wagiminator/ATmega-Soldering-Station/software/UI_upgrade_by_createskyblue/img/J3F}W4XX_3]NT2K_JGCY}(J.jpg

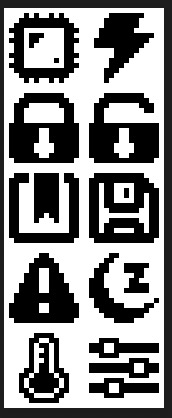
software/UI_upgrade_by_createskyblue/img/J3F}W4XX_3]NT2K_JGCY}(J.jpg
