wagiminator/ATmega-Soldering-Station/software/UI_upgrade_by_createskyblue/img/PixeSymbol3字符映射表.png

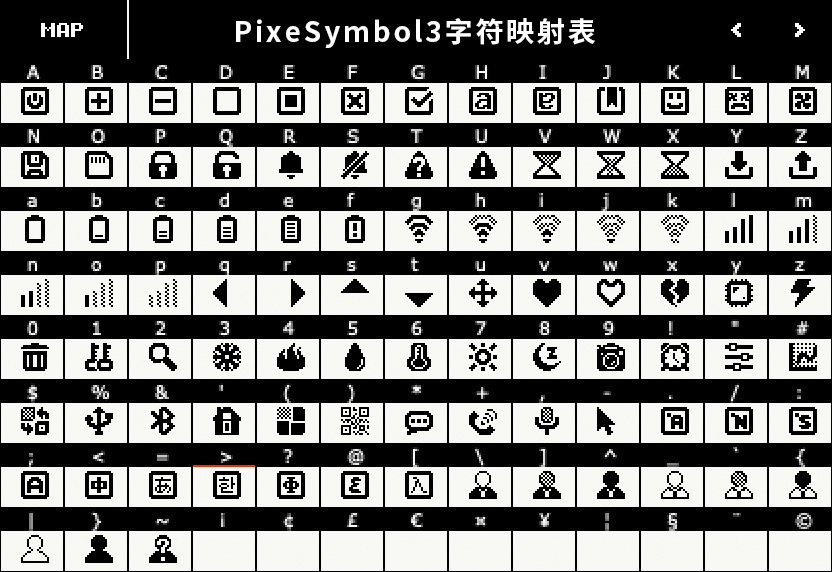
software/UI_upgrade_by_createskyblue/img/PixeSymbol3字符映射表.png
