wagiminator/ATmega-Soldering-Station/software/UI_upgrade_by_createskyblue/Program/1.8/1.8t4/1.8t4.ino

/*License: http://creativecommons.org/licenses/by-sa/3.0/
   采用CC3.0协议共享此程序
   您可以自由地
  共享 — 在任何媒介以任何形式复制、发行本作品
  演绎 — 修改、翻译或以本作品为基础进行创作
  在任何用途下，甚至商业目的。
  本许可协议为“自由文化作品（Free Cultural Works）”所接受。
  只要你遵守许可协议条款，许可人就无法收回你的这些权利。

  Attribution-ShareAlike 3.0 Unported (CC BY-SA 3.0)
  This is a human-readable summary of (and not a substitute for) the license. Disclaimer.
  You are free to:
  Share — copy and redistribute the material in any medium or format
  Adapt — remix, transform, and build upon the material
  for any purpose, even commercially.
  This license is acceptable for Free Cultural Works.
  The licensor cannot revoke these freedoms as long as you follow the license terms.
*/
// SolderingStation2
//
// ATmega328-controlled Soldering Station for Hakko T12 Tips.
// 此v1.8t4版本功能简介
// This 1.8t4 version of the code implements:
// - 烙铁头温度实时监测
// - Temperature measurement of the tip
// - PID温度控制
// - Direct or PID control of the heater
// - 可以通过编码器进行控制温度
// - Temperature control via rotary encoder
// - 短按编码器进入短时升温模式
// - Boost mode by short pressing rotary encoder switch
// - 长按编码器进入主菜单
// - Setup menu by long pressing rotary encoder switch
// - 手柄震动检测（需要手柄含有震动传感器）
// - Handle movement detection (by checking ball switch)
// - 手柄连接检测（通过判断烙铁头温度是否能够被读取来实现）
// - Iron unconnected detection (by idenfying invalid temperature readings)
// - 定时器设定 - 随眠，关机时间
// - Time driven sleep/power off mode if iron is unused (movement detection)
// - 可以测量主控芯片电压以及温度
// - Measurement of input voltage, Vcc and ATmega's internal temperature
// - 在OLED上实现信息显示
// - Information display on OLED
// - 支持无源蜂鸣器
// - Buzzer
// - 允许设置不同烙铁头的温度校准值
// - Calibrating and managing different soldering tips
// - 设置被保存在EEPROM，掉电不丢失
// - Storing user settings into the EEPROM
// - 允许热插拔烙铁头，并弹出烙铁头配置选择菜单
// - Tip change detection
// - 芯片过热以及低电压报警
// - Chip overheating and low voltage alarm
// - 更好的实时温度条以及实时功率条
// - Better real-time temperature bar and real-time power bar
// - 拥有过渡动画
// - Have transition animation
// - 内置屏幕保护程序
// - Built in screen saver
// - 屏幕翻转设置
// - Screen flip settings
// - 内置英文、中文、日文语言包
// - Built in English, Chinese and Japanese language pack
// - 开机密码设置
// - System Password
// - 允许设置旋钮方向
// - Knob direction setting menu
// - 内嵌看门狗，宕机自动重启
// - Watchdog timer automatic reset the MCU

// Power supply should be in the range of 16V/2A to 24V/3A and well
// stabilized.
//
// For calibration you need a soldering iron tips thermometer. For best results
// wait at least three minutes after switching on the soldering station before
// you start the calibration process.
//
// Controller:  ATmega328p
// Core:        Barebones ATmega (https://github.com/carlosefr/atmega)
// Clockspeed:  16 MHz external
//
// 2019/2020 by Stefan Wagner with great support from John Glavinos
// 2020-8 UI upgrade by LHW-createskyblue 、lihaoyun6
// Project Page: https://easyeda.com/wagiminator

//关于界面-项目页面二维码 ->为了加入欠压报警只能阉割掉关于页面的二维码
//const unsigned char QRCode[] PROGMEM = { 0x00, 0x00, 0x3e, 0x0e, 0x7c, 0x0c, 0x00, 0x00, 0x00, 0x00, 0x3e, 0x0e, 0x7c, 0x0c, 0x00, 0x00, 0x00, 0x00, 0x3e, 0x0e, 0x7c, 0x0c, 0x00, 0x00, 0x1f, 0xfe, 0x3f, 0xc1, 0x8c, 0x0c, 0x7f, 0xf8, 0x1f, 0xfe, 0x3f, 0xc1, 0x8c, 0x0c, 0x7f, 0xf8, 0x18, 0x06, 0x30, 0x01, 0xf3, 0x8c, 0x60, 0x18, 0x18, 0x06, 0x30, 0x01, 0xf3, 0x8c, 0x60, 0x18, 0x18, 0x06, 0x30, 0x01, 0xf3, 0x8c, 0x60, 0x18, 0x18, 0x06, 0x3e, 0x0f, 0xf0, 0x0c, 0x60, 0x18, 0x18, 0x06, 0x3e, 0x0f, 0xf0, 0x0c, 0x60, 0x18, 0x18, 0x06, 0x3f, 0xc1, 0xf0, 0x0c, 0x60, 0x18, 0x18, 0x06, 0x3f, 0xc1, 0xf0, 0x0c, 0x60, 0x18, 0x18, 0x06, 0x3f, 0xc1, 0xf0, 0x0c, 0x60, 0x18, 0x1f, 0xfe, 0x3e, 0x30, 0x70, 0x0c, 0x7f, 0xf8, 0x1f, 0xfe, 0x3e, 0x30, 0x70, 0x0c, 0x7f, 0xf8, 0x00, 0x00, 0x31, 0xce, 0x73, 0x8c, 0x00, 0x00, 0x00, 0x00, 0x31, 0xce, 0x73, 0x8c, 0x00, 0x00, 0x00, 0x00, 0x31, 0xce, 0x73, 0x8c, 0x00, 0x00, 0xff, 0xff, 0xf0, 0x01, 0x83, 0x8f, 0xff, 0xff, 0xff, 0xff, 0xf0, 0x01, 0x83, 0x8f, 0xff, 0xff, 0x00, 0xc0, 0x01, 0xc1, 0x8c, 0x00, 0x7f, 0x1f, 0x00, 0xc0, 0x01, 0xc1, 0x8c, 0x00, 0x7f, 0x1f, 0x00, 0xc0, 0x01, 0xc1, 0x8c, 0x00, 0x7f, 0x1f, 0x07, 0xc7, 0xcf, 0xce, 0x7f, 0x8c, 0x1f, 0xf8, 0x07, 0xc7, 0xcf, 0xce, 0x7f, 0x8c, 0x1f, 0xf8, 0x07, 0xc7, 0xcf, 0xce, 0x7f, 0x8c, 0x1f, 0xf8, 0xf8, 0x00, 0x3e, 0x3e, 0x03, 0xf0, 0x7f, 0x00, 0xf8, 0x00, 0x3e, 0x3e, 0x03, 0xf0, 0x7f, 0x00, 0xe0, 0xc7, 0xcf, 0xfe, 0x03, 0x80, 0x1f, 0xe7, 0xe0, 0xc7, 0xcf, 0xfe, 0x03, 0x80, 0x1f, 0xe7, 0xe0, 0xc7, 0xcf,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
const unsigned char Lang_JP[] PROGMEM = { 0x80, 0x04, 0x00, 0x00, 0x3f, 0xf0, 0x3d, 0xf0, 0x20, 0x10, 0x3b, 0xf0, 0x3b, 0x70, 0x30, 0x30, 0x2b, 0x50, 0x2a, 0xd0, 0x31, 0xb0, 0x3f, 0xf0, 0x00, 0x00, 0x80, 0x04 };
const unsigned char Save[] PROGMEM = { 0x00, 0x04, 0x58, 0x08, 0x58, 0x08, 0x58, 0x08, 0x40, 0x08, 0x7f, 0xf8, 0x60, 0x18, 0x5f, 0xe8, 0x5b, 0x68, 0x5f, 0xe8, 0x5b, 0x68, 0x1c, 0xe8, 0x5f, 0xe8, 0x00, 0x00 };
const unsigned char Lock[] PROGMEM = { 0xe0, 0x1c, 0xc0, 0x0c, 0x8f, 0xc4, 0x9f, 0xe4, 0x9f, 0xe4, 0x9f, 0xe4, 0x00, 0x00, 0x03, 0x00, 0x03, 0x00, 0x03, 0x00, 0x07, 0x80, 0x07, 0x80, 0x03, 0x00, 0x80, 0x04 };
const unsigned char Set19[] PROGMEM = { 0xf8, 0x7c, 0x80, 0x04, 0xbc, 0xf4, 0x3f, 0xf0, 0x38, 0x70, 0xb7, 0xb4, 0xb6, 0xb4, 0xb5, 0xb4, 0xb7, 0xb4, 0x38, 0x70, 0x3f, 0xf0, 0xbc, 0xf4, 0x80, 0x04, 0xf8, 0x7c };
const unsigned char *Ico_table[] = {
  Set0, Set1, Set2, Set3, Set4, Set5, Set19, Set6, Lock, Set_LANG, QRC, Set7,
  Set8, Set9, Set0, Set10, Set12, Save,
  Set0, Set11, Set14, Save,
  Set11, Set13, Set14, Save,
  Set15, Set16,
  Set17, Set18, //5
  Set5_1, Set5,
  c_NO, Set7,
  Lang_CN, Lang_EN, Lang_JP, //8
  Set4, Set4F, Save,
};
const byte Menu_table[] = {12, 6, 4, 4, 2, 2, 2, 2, 3, 3}; //菜单 标签 温控 定时 控制方式 首页 蜂鸣器 标签删除确认界面 语言菜单 翻转 显示
byte MenuLevel = 0; //菜单层级

/*////////////////////////////////////////////////////////////////////////////////////////////////////
   多语言支持
   Multilingual support
   ///////////////////////////////////////////////////////////////////////////////////////////////////
*/
/*
    英语库  ENGLISH
*/
const char EN_0[] PROGMEM = "Tip";
const char EN_1[] PROGMEM = "Temp";
const char EN_2[] PROGMEM = "Timer";
const char EN_3[] PROGMEM = "Control";
const char EN_4[] PROGMEM = "Screen";
const char EN_5[] PROGMEM = "Buzzer";
const char EN_6[] PROGMEM = "LOW Vol";
const char EN_7[] PROGMEM = "Lang";
const char EN_8[] PROGMEM = "Return";
const char EN_9[] PROGMEM = "Change";
const char EN_10[] PROGMEM = "Calibrate";
const char EN_11[] PROGMEM = "Rename";
const char EN_12[] PROGMEM = "Delete";
const char EN_13[] PROGMEM = "Add";
const char EN_14[] PROGMEM = "Save";
const char EN_15[] PROGMEM = "Default";
const char EN_16[] PROGMEM = "Sleep";
const char EN_17[] PROGMEM = "Boost";
const char EN_18[] PROGMEM = "Save";
const char EN_19[] PROGMEM = "Sleep";
const char EN_20[] PROGMEM = "Off";
const char EN_21[] PROGMEM = "Boost";
const char EN_22[] PROGMEM = "Save";
const char EN_23[] PROGMEM = "Direct";
const char EN_24[] PROGMEM = "PID";
const char EN_25[] PROGMEM = "Big";
const char EN_26[] PROGMEM = "Infos";
const char EN_27[] PROGMEM = "OFF";
const char EN_28[] PROGMEM = "ON";
const char EN_29[] PROGMEM = "NO";
const char EN_30[] PROGMEM = "YES";
const char EN_31[] PROGMEM = "CN";
const char EN_32[] PROGMEM = "EN";
const char EN_33[] PROGMEM = "NO";
const char EN_34[] PROGMEM = "OK";
const char EN_35[] PROGMEM = "Main Screen";
const char EN_36[] PROGMEM = "Flip";
const char EN_37[] PROGMEM = "Save";
const char EN_38[] PROGMEM = "About";
const char EN_39[] PROGMEM = "JP";
const char EN_40[] PROGMEM = "Lock";
const char EN_41[] PROGMEM = "Rotary";
const char *const EN_table[] PROGMEM = {EN_0, EN_1, EN_2, EN_3, EN_4, EN_5, EN_41, EN_6, EN_40, EN_7, EN_38, EN_8, EN_9, EN_10, EN_11, EN_12, EN_13, EN_14, EN_15, EN_16, EN_17, EN_18, EN_19, EN_20, EN_21, EN_22, EN_23, EN_24, EN_25, EN_26, EN_27, EN_28, EN_29, EN_30, EN_31, EN_32, EN_39, EN_35, EN_36, EN_37,};

/*
  #!/usr/bin/python
  # -*- coding: UTF-8 -*-
  for num in range(0,38):
  print("EN_",end="")
  print(num,end='')
  print(",",end="")
*/
/*
    中文语言库 CHINESE

  ////////////////////////////////////////////////////////////////////////////////////////////////////////
   本地化提示：你可以按照位图的大小，把这里的文字位图替换成你的语言，确保位图分辨率一致即可，我们欢迎你把程序翻译为你当地的语言！
  Localization tips: you can according to the size of the bitmap,
  replace the text bitmap here with your language,
  ensure that the bitmap resolution is consistent,
  we welcome you to translate the program into your local language!
  ////////////////////////////////////////////////////////////////////////////////////////////////////////
*/
//width:28,height:14 主界面中文提示
//Main Screen
//错误-ERROR
const unsigned char S1[] PROGMEM = { 0x20, 0x92, 0x1f, 0xc0, 0x3d, 0xf9, 0x90, 0x40, 0x20, 0x90, 0x90, 0x40, 0x40, 0x90, 0x1f, 0xc0, 0x7b, 0xff, 0x00, 0x00, 0xa0, 0x01, 0x3f, 0xe0, 0x21, 0xf9, 0x02, 0x00, 0xfd, 0x09, 0x02, 0x00, 0x21, 0x09, 0x7f, 0xf0, 0x21, 0xf9, 0x05, 0x00, 0x21, 0x09, 0x45, 0x00, 0x29, 0x09, 0x88, 0x80, 0x31, 0xf9, 0x10, 0x70, 0x21, 0x08, 0x20, 0x20 };
//关机-OFF
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
};
/*
  プリセット
  温度調節
  タイマー
  コントロール
  スクリーン
  ブザー
  低電圧アラーム
  言語
  戻る
  取り替える
  キャリブレーション
  名前を変更
  削除
  追加
  保存
  デフォルト
  睡眠
  ブースト
  保存
  睡眠
  閉じる
  ブースト
  保存
  ダイレクト
  PID
  ビッグ
  ニュース
  閉じる
  開く
  いいえ、
  はい、
  中国語
  英語
  いいえ、
  はい、
  メインスクリーン
  フリップ
  保存
  アバウト
  日本語
  つまみ方向

  汉字转换表:温度調節低電圧言語戻取替名前変更削除追加保存睡眠閉開中国英日本密碼
*/
const char JP_0[] PROGMEM  = { 0xf0, 0xcc, 0xdf, 0xb0, 0xb8, 0xbd, };
const char JP_1[] PROGMEM  = { 0xf2, 0x00, 0x01, 0x02, 0x03, };
const char JP_2[] PROGMEM  = { 0xf0, 0xb4, 0x99, 0xd3, 0xee, };
const char JP_3[] PROGMEM  = { 0xf0, 0xa8, 0xe8, 0xbd, 0xe2, 0xee, 0xe0, };
const char JP_4[] PROGMEM  = { 0xf0, 0xae, 0xa4, 0xdf, 0xee, 0xe8, };
const char JP_5[] PROGMEM  = { 0xf0, 0xcb, 0xab, 0xee, };
const char JP_6[] PROGMEM  = { 0xf2, 0x04, 0x05, 0x06, 0xf0, 0x97, 0xde, 0xee, 0xd5, };
const char JP_7[] PROGMEM  = { 0xf2, 0x07, 0x08, };
const char JP_8[] PROGMEM  = { 0xf2, 0x09, 0xf0, 0x8d, };
const char JP_9[] PROGMEM  = { 0xf2, 0x0a, 0xf0, 0x8c, 0xf2, 0x0b, 0xf0, 0x4a, 0x8d, };
const char JP_10[] PROGMEM = { 0xf0, 0xa2, 0xd8, 0xdf, 0xcb, 0xe1, 0xee, 0xac, 0xdc, 0xe8, };
const char JP_11[] PROGMEM = { 0xf2, 0x0c, 0x0d, 0xf0, 0x94, 0xf2, 0x0e, 0x0f, };
const char JP_12[] PROGMEM = { 0xf2, 0x10, 0x11, };
const char JP_13[] PROGMEM = { 0xf2, 0x12, 0x13, };
const char JP_14[] PROGMEM = { 0xf2, 0x14, 0x15, };
const char JP_15[] PROGMEM = { 0xf0, 0xbc, 0xca, 0x9e, 0xe0, 0xbd, };
const char JP_16[] PROGMEM = { 0xf2, 0x16, 0x17, };
const char JP_17[] PROGMEM = { 0xf0, 0xcb, 0xee, 0xae, 0xbd, };
const char JP_18[] PROGMEM = { 0xf2, 0x14, 0x15, };
const char JP_19[] PROGMEM = { 0xf2, 0x16, 0x17, };
const char JP_20[] PROGMEM = { 0xf2, 0x18, 0xf0, 0x5a, 0x8d, };
const char JP_21[] PROGMEM = { 0xf0, 0xcb, 0xee, 0xae, 0xbd, };
const char JP_22[] PROGMEM = { 0xf2, 0x14, 0x15, };
const char JP_23[] PROGMEM = { 0xf0, 0xb5, 0x99, 0xe1, 0xa4, 0xbd, };
const char JP_24[] PROGMEM = { 0xf1, 0x30, 0x29, 0x24, };
const char JP_25[] PROGMEM = { 0xf0, 0xc8, 0xb8, 0xa5, };
const char JP_26[] PROGMEM = { 0xf0, 0xc0, 0xda, 0xee, 0xae, };
const char JP_27[] PROGMEM = { 0xf2, 0x18, 0xf0, 0x5a, 0x8d, };
const char JP_28[] PROGMEM = { 0xf2, 0x19, 0xf0, 0x51, };
const char JP_29[] PROGMEM = { 0xf0, 0x46, 0x46, 0x4a, 0x01, };
const char JP_30[] PROGMEM = { 0xf0, 0x71, 0x46, 0x01, };
const char JP_31[] PROGMEM = { 0xf2, 0x1a, 0x1b, 0x08, };
const char JP_32[] PROGMEM = { 0xf2, 0x1c, 0x08, };
const char JP_33[] PROGMEM = { 0xf0, 0x46, 0x46, 0x4a, 0x01, };
const char JP_34[] PROGMEM = { 0xf0, 0x71, 0x46, 0x01, };
const char JP_35[] PROGMEM = { 0xf0, 0xd6, 0x99, 0xe8, 0xae, 0xa4, 0xdf, 0xee, 0xe8, };
const char JP_36[] PROGMEM = { 0xf0, 0xca, 0xdf, 0xb8, 0xcc, };
const char JP_37[] PROGMEM = { 0xf2, 0x14, 0x15, };
const char JP_38[] PROGMEM = { 0xf0, 0x97, 0xc5, 0x9b, 0xbd, };
const char JP_39[] PROGMEM = { 0xf2, 0x1d, 0x1e, 0x08, };
const char JP_40[] PROGMEM = { 0xf2, 0x1f, 0x20, }; //密码
const char JP_41[] PROGMEM = { 0xf0, 0x66, 0x80, 0x81, 0xf2, 0x21, 0x22, }; //つまみ方向
const char *const JP_table[] = {JP_0, JP_1, JP_2, JP_3, JP_4, JP_5, JP_41, JP_6, JP_40, JP_7, JP_38, JP_8, JP_9, JP_10, JP_11, JP_12, JP_13, JP_14, JP_15, JP_16, JP_17, JP_18, JP_19, JP_20, JP_21, JP_22, JP_23, JP_24, JP_25, JP_26, JP_27, JP_28, JP_29, JP_30, JP_31, JP_32, JP_39, JP_35, JP_36, JP_37,};
const char JP_Length_table[] PROGMEM = {6, 5, 5, 7, 6, 4, 7, 9, 3, 3 , 5, 4, 9, 10, 8, 3, 3, 3, 6, 3, 5, 3, 3, 5, 5, 3, 6, 4, 4, 5, 5, 4, 5, 4, 4, 3, 4,  9, 5, 3,};

#endif

bool lastbutton;
#include <Arduboy2.h>  //注意 这里使用被阉割的图形库，只有绘图功能，并非通用的版本
Arduboy2 arduboy;

#include <EEPROM.h>
#include <PID_v1.h>
#include <avr/sleep.h>

// Firmware version
#define VERSION       "v1.8t4"

// Type of rotary encoder
#define ROTARY_TYPE   1         // 0: 2 increments/step; 1: 4 increments/step

// Pins
#define SENSOR_PIN    A0        // temperature sense
#define VIN_PIN       A1        // input voltage sense
#define BUZZER_PIN     5        // buzzer
#define BUTTON_PIN     6        // rotary encoder switch
#define ROTARY_1_PIN   7        // rotary encoder 1
#define ROTARY_2_PIN   8        // rotary encoder 2
#define CONTROL_PIN    9        // heater MOSFET PWM control
#define SWITCH_PIN    10        // handle vibration switch

// Default temperature control values (recommended soldering temperature: 300-380°C)
#define ChipTempCalVal 335  //芯片内部温度读取校准值 -->可以根据实际情况修改，不同机器情况不同，通常误差在10°C内
#define TEMP_MIN      150       // min selectable temperature
#define TEMP_MAX      400       // max selectable temperature
#define TEMP_DEFAULT  320       // default start setpoint
#define TEMP_SLEEP    150       // temperature in sleep mode
#define TEMP_BOOST     60       // temperature increase in boost mode
#define TEMP_STEP      10       // rotary encoder temp change steps

// Default tip temperature calibration values
#define TEMP200       216       // temperature at ADC = 200
#define TEMP280       308       // temperature at ADC = 280
#define TEMP360       390       // temperature at ADC = 360
#define TEMPCHP       30        // chip temperature while calibration
#define TIPMAX        8         // max number of tips
#define TIPNAMELENGTH 6         // max length of tip names (including termination)
#define TIPNAME       "BC1.5"   // default tip name

// Default timer values (0 = disabled)
#define TIME2SLEEP     5        // time to enter sleep mode in minutes
#define TIME2OFF      15        // time to shut off heater in minutes
#define TIMEOFBOOST   40        // time to stay in boost mode in seconds

// Control values
#define TIME2SETTLE   950       // time in microseconds to allow OpAmp output to settle
#define SMOOTHIE      0.05      // OpAmp output smooth factor (1=no smoothing; 0.05 default)
#define PID_ENABLE    true      // enable PID control
#define BEEP_ENABLE   true      // enable/disable buzzer
#define MAINSCREEN    1         // type of main screen (0: big numbers; 1: more infos)

// EEPROM identifier
#define EEPROM_IDENT   0x140A   // to identify if EEPROM was written by this program

//Beep
#define SetBeepCoolTime 200
unsigned long BeepCoolTime;

// Define the aggressive and conservative PID tuning parameters
double aggKp = 11, aggKi = 0.5, aggKd = 1;
double consKp = 11, consKi = 3, consKd = 5;

// Default values that can be changed by the user and stored in the EEPROM
uint16_t  DefaultTemp = TEMP_DEFAULT;
uint16_t  SleepTemp   = TEMP_SLEEP;
uint8_t   BoostTemp   = TEMP_BOOST;
uint8_t   time2sleep  = TIME2SLEEP;
uint8_t   time2off    = TIME2OFF;
uint8_t   timeOfBoost = TIMEOFBOOST;
uint8_t   MainScrType = MAINSCREEN;
bool      PIDenable   = PID_ENABLE;
bool      beepEnable  = BEEP_ENABLE;
// Default values for tips
uint16_t  CalTemp[TIPMAX][4] = {TEMP200, TEMP280, TEMP360, TEMPCHP};
char      TipName[TIPMAX][TIPNAMELENGTH] = {TIPNAME};
uint8_t   CurrentTip   = 0;
uint8_t   NumberOfTips = 1;

// Menu items
/*
   这个可以选择进行界面美化
  const char *DeleteMessage[]    = { "Warning", "You cannot", "delete your", "last tip!" };
  const char *MaxTipMessage[]    = { "Warning", "You reached", "maximum number", "of tips!" };
*/
// Variables for pin change interrupt
volatile uint8_t  a0, b0, c0, d0;
volatile bool     ab0;
volatile int      count, countMin, countMax, countStep;
volatile bool     handleMoved;

// Variables for temperature control
uint16_t  SetTemp, ShowTemp, gap, Step;
double    Input, Output, Setpoint, RawTemp, CurrentTemp, ChipTemp;

// Variables for voltage readings
uint16_t  Vcc, Vin;

// State variables
bool      inSleepMode = false;
bool      inOffMode   = false;
bool      inBoostMode = false;
bool      inCalibMode = false;
bool      isWorky     = true;
bool      beepIfWorky = true;
bool      TipIsPresent = true;
bool      FlipState = false;
// Timing variables
uint32_t  sleepmillis;
uint32_t  boostmillis;
uint32_t  buttonmillis;
uint8_t   goneMinutes;
uint8_t   goneSeconds;
uint8_t   SensorCounter = 255;
//串口助手
int x, y, a, b;
//欠压报警
byte UnderVoltage = 0;
// Control variables
uint16_t  time2settle = 300;

//模拟数字滚轮 Numerical scrolling effect
int Value;
int LastValue[3];
float SlidingAnimationY[3];

//开机密码 BootPassword
int Password = 0;

//屏幕保护-主题：密集运算
byte Line[4];

//编码器旋转调整方向设定
bool RotaryD = false;

// Specify the links and initial PID tuning parameters
PID ctrl(&Input, &Output, &Setpoint, aggKp, aggKi, aggKd, REVERSE);

//NMOS - PMOS软件切换
#define UsePMOS false

//LANG 语言支持
/*  0 - 中文 CHINESE
    1 - 英文 ENGLISH
    2 - 日语
*/
byte LANG = 0;
void Flip(bool Fmode) {
  arduboy.flipVertical(Fmode);
  arduboy.flipHorizontal(Fmode);
}

ISR(WDT_vect)  //WDT中断，8秒一次
{
  WDTCSR |= _BV(WDIE);
}

void setup() {
  //设置看门狗自动复位
  SetWDT();
  //启动arduboy
  arduboy.begin();
  arduboy.setFrameRate(30);

  //Serial.begin(115200);
  // set the pin modes

  //设置IO
  pinMode(SENSOR_PIN,   INPUT);
  pinMode(VIN_PIN,      INPUT);
  pinMode(BUZZER_PIN,   OUTPUT);
  pinMode(CONTROL_PIN,  OUTPUT);
  pinMode(ROTARY_1_PIN, INPUT_PULLUP);
  pinMode(ROTARY_2_PIN, INPUT_PULLUP);
  pinMode(BUTTON_PIN,   INPUT_PULLUP);
  pinMode(SWITCH_PIN,   INPUT_PULLUP);
#if UsePMOS
  analogWrite(CONTROL_PIN, 0);
#else
  analogWrite(CONTROL_PIN, 255);        // this shuts off the heater
#endif
  digitalWrite(BUZZER_PIN, LOW);        // must be LOW when buzzer not in use

  // setup ADC  初始化ADC
  ADCSRA |= bit (ADPS0) | bit (ADPS1) | bit (ADPS2);  // set ADC prescaler to 128
  ADCSRA |= bit (ADIE);                 // enable ADC interrupt
  interrupts ();                        // enable global interrupts

  // setup pin change interrupt for rotary encoder 初始化编码器IO
  PCMSK0 = bit (PCINT0);                // Configure pin change interrupt on Pin8
  PCICR  = bit (PCIE0);                 // Enable pin change interrupt
  PCIFR  = bit (PCIF0);                 // Clear interrupt flag


  // get default values from EEPROM
  getEEPROM();
  //设置屏幕反转状态
  Flip(FlipState);
  //初始化屏幕保护动画
  for (byte a = 0; a < 4; a++) Line[a] = 32 * a;
  //开机密码
  BootPassword();

  // read supply voltages in mV
  Vcc = getVCC(); Vin = getVIN();

  // read and set current iron temperature
  SetTemp  = DefaultTemp;
  RawTemp  = denoiseAnalog(SENSOR_PIN);
  ChipTemp = getChipTemp();
  calculateTemp();

  // turn on heater if iron temperature is well below setpoint
#if UsePMOS
  if ((CurrentTemp + 20) < DefaultTemp) analogWrite(CONTROL_PIN, 255);
#else
  if ((CurrentTemp + 20) < DefaultTemp) analogWrite(CONTROL_PIN, 0);
#endif


  // tell the PID to range between 0 and the full window size
  ctrl.SetOutputLimits(0, 255);

  // start PID
  ctrl.SetMode(AUTOMATIC);

  // set initial rotary encoder values
  a0 = PINB & 1; b0 = PIND >> 7 & 1; ab0 = (a0 == b0);
  setRotary(TEMP_MIN, TEMP_MAX, TEMP_STEP, DefaultTemp);

  // reset sleep timer
  sleepmillis = millis();

  // long beep for setup completion
  beep(); beep();

}


void loop() {
  //HelpMeSerialer();
  ROTARYCheck();      // check rotary encoder (temp/boost setting, enter setup menu)
  SLEEPCheck();       // check and activate/deactivate sleep modes
  SENSORCheck();      // reads temperature and vibration switch of the iron
  Thermostat();       // heater control
  MainScreen();       // updates the main page on the OLED
  //beep(0);
}




// check rotary encoder; set temperature, toggle boost mode, enter setup menu accordingly
void ROTARYCheck() {
  // set working temperature according to rotary encoder value
  SetTemp = getRotary();

  // check rotary encoder switch
  uint8_t c = digitalRead(BUTTON_PIN);
  if ( !c && c0 ) {
    beep();
    buttonmillis = millis();
    while ( (!digitalRead(BUTTON_PIN)) && ((millis() - buttonmillis) < 500) );
    if ((millis() - buttonmillis) >= 500) SetupScreen();
    else {
      inBoostMode = !inBoostMode;
      if (inBoostMode) boostmillis = millis();
      handleMoved = true;
    }
  }
  c0 = c;

  // check timer when in boost mode
  if (inBoostMode && timeOfBoost) {
    goneSeconds = (millis() - boostmillis) / 1000;
    if (goneSeconds >= timeOfBoost) {
      inBoostMode = false;              // stop boost mode
      beep();                           // beep if boost mode is over
      beepIfWorky = true;               // beep again when working temperature is reached
    }
  }
}


// check and activate/deactivate sleep modes
void SLEEPCheck() {
  if (handleMoved) {                    // if handle was moved
    if (inSleepMode) {                  // in sleep or off mode?
      if ((CurrentTemp + 20) < SetTemp) // if temp is well below setpoint

        // then start the heater right now

#if UsePMOS
        analogWrite(CONTROL_PIN, 255);
#else
        analogWrite(CONTROL_PIN, 0);
#endif

      beep();                           // beep on wake-up
      beepIfWorky = true;               // beep again when working temperature is reached
    }
    handleMoved = false;                // reset handleMoved flag
    inSleepMode = false;                // reset sleep flag
    inOffMode   = false;                // reset off flag
    sleepmillis = millis();             // reset sleep timer
  }

  // check time passed since the handle was moved
  goneMinutes = (millis() - sleepmillis) / 60000;
  if ( (!inSleepMode) && (time2sleep > 0) && (goneMinutes >= time2sleep) ) {
    inSleepMode = true;
    beep();
  }
  if ( (!inOffMode)   && (time2off   > 0) && (goneMinutes >= time2off  ) ) {
    inOffMode   = true;
    beep();
  }
}


// reads temperature, vibration switch and supply voltages
void SENSORCheck() {
  // shut off heater in order to measure temperature
#if UsePMOS
  analogWrite(CONTROL_PIN, 0);
#else
  analogWrite(CONTROL_PIN, 255);
#endif
  delayMicroseconds(time2settle);             // wait for voltage to settle

  uint16_t temp = denoiseAnalog(SENSOR_PIN);  // read ADC value for temperature
  uint8_t d = digitalRead(SWITCH_PIN);        // check handle vibration switch
  if (d != d0) {
    handleMoved = true;  // set flag if handle was moved
    d0 = d;
  }
  if (! SensorCounter--) Vin = getVIN();      // get Vin every now and then

  // turn on again heater

#if UsePMOS
  analogWrite(CONTROL_PIN, 255 - Output);
#else
  analogWrite(CONTROL_PIN, Output);
#endif


  RawTemp += (temp - RawTemp) * SMOOTHIE;     // stabilize ADC temperature reading
  calculateTemp();

  // stabilize displayed temperature when around setpoint
  if ((ShowTemp != Setpoint) || (abs(ShowTemp - CurrentTemp) > 5)) ShowTemp = CurrentTemp;
  if (abs(ShowTemp - Setpoint) <= 1) ShowTemp = Setpoint;
  // set state variable if temperature is in working range; beep if working temperature was just reached
  gap = abs(SetTemp - CurrentTemp);
  if (gap < 5) {
    if (!isWorky && beepIfWorky) beep();
    isWorky = true;
    beepIfWorky = false;
  } else {
    isWorky = false;
    beepIfWorky = true;
  }
  // checks if tip is present or currently inserted
  if (ShowTemp > 500) TipIsPresent = false;   // tip removed ?
  if (!TipIsPresent && (ShowTemp < 500)) {    // new tip inserted ?
    //关闭加热
#if UsePMOS
    analogWrite(CONTROL_PIN, 0);
#else
    analogWrite(CONTROL_PIN, 255);
#endif
    beep();                                   // beep for info
    TipIsPresent = true;                      // tip is present now
    ChangeTipScreen();                        // show tip selection screen
    updateEEPROM();                           // update setting in EEPROM
    handleMoved = true;                       // reset all timers
    RawTemp  = denoiseAnalog(SENSOR_PIN);     // restart temp smooth algorithm
    c0 = LOW;                                 // switch must be released
    setRotary(TEMP_MIN, TEMP_MAX, TEMP_STEP, SetTemp);  // reset rotary encoder
  }
}


// calculates real temperature value according to ADC reading and calibration values
void calculateTemp() {
  if      (RawTemp < 200) CurrentTemp = map (RawTemp,   0, 200,                     21, CalTemp[CurrentTip][0]);
  else if (RawTemp < 280) CurrentTemp = map (RawTemp, 200, 280, CalTemp[CurrentTip][0], CalTemp[CurrentTip][1]);
  else                    CurrentTemp = map (RawTemp, 280, 360, CalTemp[CurrentTip][1], CalTemp[CurrentTip][2]);
}


//调温
void Thermostat() {
  // define Setpoint acoording to current working mode
  if      (inOffMode)   Setpoint = 0;
  else if (inSleepMode) Setpoint = SleepTemp;
  else if (inBoostMode) Setpoint = SetTemp + BoostTemp;
  else                  Setpoint = SetTemp;

  // control the heater (PID or direct)
  gap = abs(Setpoint - CurrentTemp);
  if (PIDenable) {
    Input = CurrentTemp;
    if (gap < 30) ctrl.SetTunings(consKp, consKi, consKd);
    else ctrl.SetTunings(aggKp, aggKi, aggKd);
    ctrl.Compute();
  } else {
    // turn on heater if current temperature is below setpoint
    if ((CurrentTemp + 0.5) < Setpoint) Output = 0; else Output = 255;
  }
  // set heater PWM
#if UsePMOS
  analogWrite(CONTROL_PIN, 255 - Output);
#else
  analogWrite(CONTROL_PIN, Output);
#endif
}


// creates a short beep on the buzzer
void beep() {
  /*
    if (beepEnable) {
    if (BeepCoolTime + SetBeepCoolTime < millis()) {
      if (state) BeepCoolTime = millis();
      analogWrite(BUZZER_PIN, 0);
    }  else analogWrite(BUZZER_PIN, 127);
    } else analogWrite(BUZZER_PIN, 0);
  */
  //体谅一下，没内存了，只能用原始的办法驱动无源蜂鸣器，否则我也不想牺牲宝贵响应资源换内存
  if (beepEnable) {
    for (uint8_t i = 0; i < 255; i++) {
      digitalWrite(BUZZER_PIN, HIGH);
      delayMicroseconds(125);
      digitalWrite(BUZZER_PIN, LOW);
      delayMicroseconds(125);
    }
  }
}

//设置旋转编码器的起始值
// sets start values for rotary encoder
void setRotary(int rmin, int rmax, int rstep, int rvalue) {
  countMin  = rmin << ROTARY_TYPE;
  countMax  = rmax << ROTARY_TYPE;
  if (RotaryD) countStep = rstep; else countStep = -rstep;
  count     = rvalue << ROTARY_TYPE;
}


// reads current rotary encoder value
int getRotary() {
  return (count >> ROTARY_TYPE);
}


// reads user settings from EEPROM; if EEPROM values are invalid, write defaults
void getEEPROM() {
  uint16_t identifier = (EEPROM.read(0) << 8) | EEPROM.read(1);
  if (identifier == EEPROM_IDENT) {
    DefaultTemp = (EEPROM.read(2) << 8) | EEPROM.read(3);
    SleepTemp   = (EEPROM.read(4) << 8) | EEPROM.read(5);
    BoostTemp   =  EEPROM.read(6);
    time2sleep  =  EEPROM.read(7);
    time2off    =  EEPROM.read(8);
    timeOfBoost =  EEPROM.read(9);
    MainScrType =  EEPROM.read(10);
    PIDenable   =  EEPROM.read(11);
    beepEnable  =  EEPROM.read(12);
    CurrentTip  =  EEPROM.read(13);
    NumberOfTips = EEPROM.read(14);
    LANG = EEPROM.read(15);
    FlipState = EEPROM.read(16);
    UnderVoltage = EEPROM.read(17);
    Password = (EEPROM.read(18) << 8) | EEPROM.read(19);
    RotaryD = EEPROM.read(20);
    uint8_t i, j;
    uint16_t counter = 21;
    for (i = 0; i < NumberOfTips; i++) {
      for (j = 0; j < TIPNAMELENGTH; j++) {
        TipName[i][j] = EEPROM.read(counter++);
      }
      for (j = 0; j < 4; j++) {
        CalTemp[i][j]  = EEPROM.read(counter++) << 8;
        CalTemp[i][j] |= EEPROM.read(counter++);
      }
    }
  }
  else {
    EEPROM.update(0, EEPROM_IDENT >> 8); EEPROM.update(1, EEPROM_IDENT & 0xFF);
    updateEEPROM();
  }
}


// writes user settings to EEPROM using updade function to minimize write cycles
void updateEEPROM() {
  EEPROM.update( 2, DefaultTemp >> 8);
  EEPROM.update( 3, DefaultTemp & 0xFF);
  EEPROM.update( 4, SleepTemp >> 8);
  EEPROM.update( 5, SleepTemp & 0xFF);
  EEPROM.update( 6, BoostTemp);
  EEPROM.update( 7, time2sleep);
  EEPROM.update( 8, time2off);
  EEPROM.update( 9, timeOfBoost);
  EEPROM.update(10, MainScrType);
  EEPROM.update(11, PIDenable);
  EEPROM.update(12, beepEnable);
  EEPROM.update(13, CurrentTip);
  EEPROM.update(14, NumberOfTips);
  EEPROM.update(15, LANG);
  EEPROM.update(16, FlipState);
  EEPROM.update(17, UnderVoltage);
  EEPROM.update(18, Password >> 8);
  EEPROM.update(19, Password & 0xFF);
  EEPROM.update(20, RotaryD);
  uint8_t i, j;
  uint16_t counter = 21;
  for (i = 0; i < NumberOfTips; i++) {
    for (j = 0; j < TIPNAMELENGTH; j++) EEPROM.update(counter++, TipName[i][j]);
    for (j = 0; j < 4; j++) {
      EEPROM.update(counter++, CalTemp[i][j] >> 8);
      EEPROM.update(counter++, CalTemp[i][j] & 0xFF);
    }
  }
}
//此片段用于DEBUG
void HelpMeSerialer() {
  //串口助手
  if (Serial.available()) {
    char TmpChar = Serial.read();
    switch (TmpChar) {
      case 'x': x = Serial.parseInt();
      case 'y': y = Serial.parseInt();
      case 'a': a = Serial.parseInt();
      case 'b': b = Serial.parseInt();
    }
  }
  /*
    Serial.println(String("X ->") + x);
    Serial.println(String("Y ->") + y);
    Serial.println(String("A ->") + a);
    Serial.println(String("B ->") + b);
  */
}
// draws the main screen
void MainScreen() {
  if (!(arduboy.nextFrame())) //帧率锁
    return;
  //状态
  byte SysState;
  if (ShowTemp > 500) SysState = 0;
  else if (inOffMode) {
    SysState = 1;
    DrawIntensiveComputing();
  } else if (inSleepMode) SysState = 2;
  else if (inBoostMode) SysState = 3;
  else if (isWorky) SysState = 4;
  else if (Output < 180) SysState = 5;
  else SysState = 6;
  if (SysState != 1) {
    if (MainScrType) {
      //arduboy.invert(0);
      arduboy.clear();
      //详细信息页
      arduboy.fillRect(0, 0, 128, 64, 1); //白底
      arduboy.setTextSize(1);
      SetTextColor(0);
      //预设名
      arduboy.drawSlowXYBitmap(0, 0, Tag, 16, 16, 0);
      arduboy.setCursor(19, 4); arduboy.print(TipName[CurrentTip]);
      //显示状态
      arduboy.setCursor(53, 1);
      arduboy.setTextSize(2);
      switch (LANG) {
        case 0: arduboy.drawSlowXYBitmap(80, 1, S_table[SysState], 28, 14, 0); break;  //中文 Chinese
        default: //英文 English
          switch (SysState) {
            case 1: arduboy.print(F("OFF")); break;
            case 2: arduboy.print(F("SLEEP")); break;
            case 3: arduboy.print(F("BOOST")); break;
            case 4: arduboy.print(F("WORKY")); break;
            case 5: arduboy.print(F("HEAT")); break;
            case 6: arduboy.print(F("HOLD")); break;
            default: arduboy.print(F("ERROR")); break;
          } break;
      }
      arduboy.drawSlowXYBitmap(113, 1, C_table[SysState], 14, 14, 0);
      arduboy.setTextSize(1);
      //芯片
      //R1

      //自动报警-图标闪烁
      if (getChipTemp() < 80 || ((millis() * 4) / 1000) % 2) {
        arduboy.setCursor(19, 16); arduboy.print(getChipTemp(), 1); arduboy.print((char)248); arduboy.print(F("C")); //芯片温度
        arduboy.drawSlowXYBitmap(2, 18, Chip, 14, 14, 0);
      }
      //R2
      if ((float)Vin / 100 > UnderVoltage || ((millis() * 4) / 1000) % 2) {
        arduboy.setCursor(19, 32); arduboy.print((float)Vin / 1000, 1); arduboy.print(F("V")); //输入电压
        arduboy.drawSlowXYBitmap(2, 34, Lightning, 14, 14, 0);
      }


      //R3

      arduboy.setCursor(19, 24); arduboy.print((float)getVCC() / 1000, 2); arduboy.print(F("V")); //芯片电压

      arduboy.setCursor(19, 40); arduboy.print(F(VERSION)); //固件
      //显示探头温度
      DrawNumRect(ShowTemp);

      DrawStatusBar(0);
      arduboy.display();
      //警报声
      if (getChipTemp() > 80 && ((millis() * 4) / 1000) % 2 || (float)Vin / 100 < UnderVoltage && ((millis() * 4) / 1000) % 2) beep();
    } else {
      //arduboy.invert(1);
      arduboy.setTextSize(6);
      SetTextColor(1);
      arduboy.clear();
      if (getChipTemp() > 80 && ((millis() * 4) / 1000) % 2) beep();
      if ((float)Vin / 100 < UnderVoltage && ((millis() * 4) / 1000) % 2) beep();
      arduboy.setCursor(12, 2);

      if (ShowTemp > 500) arduboy.print(999); else arduboy.print(ShowTemp);
      arduboy.fillRect(0, 48, 128, 16, 1);

      DrawStatusBar(0);
      arduboy.display();
    }
  }
}
void DrawNumRect(int n) {
  arduboy.setCursor(57, 18);
  arduboy.setTextSize(4);
  if (ShowTemp > 500) arduboy.print(F("000")); else arduboy.print(n);
  arduboy.drawRect(55, 16, 72, 32, 0);
}
void DrawStatusBar(bool color) {
  SetTextColor(color);
  arduboy.setTextSize(1);
  //温度条
  //框
  arduboy.drawRect(1, 49, 102, 14, color);
  //条
  if (ShowTemp <= 500) arduboy.fillRect(1, 49, map(ShowTemp, 0, 500, 2, 102), 14, color);
  //指示部分
  arduboy.fillRect(map(Setpoint, 0, 500, 2, 102) - 2, 50, 3, 13, color);
  //先来个白底
  arduboy.fillRect(map(Setpoint, 0, 500, 2, 102) - 3, 60, 5, 4, color);
  arduboy.drawLine(map(Setpoint, 0, 500, 2, 102) - 1, 60, map(Setpoint, 0, 500, 2, 102) - 1, 49, !color);

  //画指示针
  arduboy.drawSlowXYBitmap(map(Setpoint, 0, 500, 2, 102) - 3, 59, Pointer, 5, 4, !color);

  //功率条
  arduboy.drawRect(104, 49, 23, 14, color);
  arduboy.fillRect(104, 49, map(Output, 255, 0, 0, 23), 14, color);

  SetTextColor(!color);
  //////////////进入反色////////////////////////////////
  arduboy.setCursor(2, 55); arduboy.print(Setpoint, 0); arduboy.print((char)248); arduboy.print(F("C")); //探头预设温度
  arduboy.setCursor(105, 55); arduboy.print(map(Output, 255, 0, 0, 100)); arduboy.print(F("%")); //功率百分比
  SetTextColor(color);
}

//设置画笔颜色
void SetTextColor(bool color) {
  arduboy.setTextBackground(!color);
  arduboy.setTextColor(color);
}
// setup screen
void SetupScreen() {
  //关闭加热
#if UsePMOS
  analogWrite(CONTROL_PIN, 0);
#else
  analogWrite(CONTROL_PIN, 255);
#endif
  beep();
  uint16_t SaveSetTemp = SetTemp;
  uint8_t selection = 0;
  bool repeat = true;

  while (repeat) {
    //arduboy.invert(0);
    MenuLevel = 0; //默认打开主菜单
    selection = MenuScreen(selection);
    switch (selection) {
      case 0:   MenuLevel = 1; TipScreen();  repeat = false; break;
      case 1:   MenuLevel = 2; TempScreen();  break;
      case 2:   MenuLevel = 3; TimerScreen();  break;
      case 3:   MenuLevel = 4; PIDenable = MenuScreen(PIDenable); break;
      case 4:   ScreenSet(); break;
      case 5:   MenuLevel = 6; beepEnable = MenuScreen(beepEnable); break;
      case 6:   RotarySet(); break;
      case 7:   UnderVoltageSet(); break;
      case 8:   PasswordSet(); break;
      case 9:   MenuLevel = 8; LANG = MenuScreen(LANG); if (LANG == 2 && !LANG_JP_State) LANG = 1; break;
      case 10:   QRcodeScreen(); break;
      default:  repeat = false; break;
    }
  }
  updateEEPROM();
  handleMoved = true;
  SetTemp = SaveSetTemp;
  setRotary(TEMP_MIN, TEMP_MAX, TEMP_STEP, SetTemp);
}

void RotarySet() {
  bool Exit = false;
  float rad;
  byte ExitBar = 0;
  SetTextColor(0);
  lastbutton = (!digitalRead(BUTTON_PIN));
  setRotary(60, 420, 18, 240);
  do {
    arduboy.setTextSize(1);
    Setpoint = getRotary();
    ShowTemp = Setpoint;

    arduboy.clear();
    //仪表盘
    arduboy.fillRect(0, 0, 128, 64, 1);
    arduboy.fillTriangle(24 + 24 * cos(rad), 24 - 24 * sin(rad), 24 + 3 * sin(rad), 24 + 3 * cos(rad), 24 - 3 * sin(rad), 24 - 3 * cos(rad), 0);
    arduboy.drawCircle(24, 24, 22, 0);
    arduboy.drawCircle(24, 24, 19, 0);
    arduboy.drawCircle(24, 24, 3, 0);
    //右上角的模式提示文本
    arduboy.setCursor(55, 1);
    arduboy.setTextSize(2);
    arduboy.print(F("MODE "));
    if (RotaryD) {
      arduboy.print(F("-"));
      rad = ((Setpoint - 60) / 360.0) * (2 * PI) - PI / 2;
    } else {
      arduboy.print(F("+"));
      rad = ((-Setpoint - 60) / 360.0) * (2 * PI) + PI * 1 / 6;
    }
    //右侧数字显示
    DrawNumRect(ShowTemp);
    //下端的状态条
    DrawStatusBar(0);
    //退出条
    arduboy.fillRect(0, 0, ExitBar, 4, 0);
    arduboy.display();
    CheckLastButton();
    if (!digitalRead(BUTTON_PIN) && !lastbutton) {
      ExitBar += 8;
      if (ExitBar > 127) Exit = true;
    } else {
      if (ExitBar > 1 && ExitBar < 64) {
        RotaryD = !RotaryD;
        setRotary(60, 420, 18, 240);
      }
      ExitBar = 0;
    }

  } while (!Exit);
  beep(); beep();
}
//显示设置菜单
// tip settings screen
void ScreenSet() {
  uint8_t selection = 0;
  bool repeat = true;
  while (repeat) {
    MenuLevel = 9;
    selection = MenuScreen(selection);
    switch (selection) {
      case 0:   MenuLevel = 5; MainScrType = MenuScreen(MainScrType);   break;
      case 1:   FlipState = !FlipState; break;
      default:  repeat = false;      break;
    }
    Flip(FlipState); //设置屏幕反转状态
  }
  updateEEPROM();
}

//预设设置菜单
// tip settings screen
void TipScreen() {
  uint8_t selection = 0;
  bool repeat = true;
  while (repeat) {
    MenuLevel = 1;
    selection = MenuScreen(selection);
    switch (selection) {
      case 0:   ChangeTipScreen();   break;
      case 1:   CalibrationScreen(); break;
      case 2:   InputNameScreen();   break;
      case 3:   DeleteTipScreen();   break;
      case 4:   AddTipScreen();      break;
      default:  repeat = false;      break;
    }
  }
}

//温控设置菜单
// temperature settings screen
void TempScreen() {
  uint8_t selection = 0;
  bool repeat = true;
  while (repeat) {
    selection = MenuScreen(selection);
    switch (selection) {
      case 0:   setRotary(TEMP_MIN, TEMP_MAX, TEMP_STEP, DefaultTemp);
        DefaultTemp = InputScreen(18); break;
      case 1:   setRotary(20, 200, TEMP_STEP, SleepTemp);
        SleepTemp = InputScreen(19); break;
      case 2:   setRotary(10, 100, TEMP_STEP, BoostTemp);
        BoostTemp = InputScreen(20); break;
      default:  repeat = false; break;
    }
  }
  updateEEPROM();
}

//定时器设置菜单
// timer settings screen
void TimerScreen() {
  uint8_t selection = 0;
  bool repeat = true;
  while (repeat) {
    selection = MenuScreen(selection);
    switch (selection) {
      case 0:   setRotary(0, 30, 1, time2sleep);
        time2sleep = InputScreen(22); break;
      case 1:   setRotary(0, 60, 5, time2off);
        time2off = InputScreen(23); break;
      case 2:   setRotary(0, 180, 10, timeOfBoost);
        timeOfBoost = InputScreen(24); break;
      default:  repeat = false; break;
    }
  }
  updateEEPROM();
}
//英语支持
void Print_EN(byte i) {
  char buffer[11];
  strcpy_P(buffer, (char *)pgm_read_word(&(EN_table[i])));
  arduboy.print(buffer);
}
//菜单界面
// menu screen
uint8_t MenuScreen(uint8_t selected) {
  int SlidingAnimationX;
  uint8_t lastselected = selected;
  setRotary(0, Menu_table[MenuLevel] - 1, 1, selected);
  lastbutton = (!digitalRead(BUTTON_PIN));
  SetTextColor(1);
  do {
    selected = getRotary();
    //非线性滑动动画
    SlidingAnimationX += (selected - lastselected) * 56;
    if (SlidingAnimationX != 0) SlidingAnimationX += 0.6 * (-SlidingAnimationX);
    lastselected = selected;
    arduboy.clear();
    //绘制图标 如果有指定的话
    for (byte i = 0; i < 5; i++) if (selected - 2 + i >= 0 && selected - 2 + i < Menu_table[MenuLevel]) DrawApp(-72 + i * 56 + SlidingAnimationX, selected - 2 + i + QueryMenuObject());
    DrawAppText(selected + QueryMenuObject());

    arduboy.display();
    CheckLastButton();
    //beep(0);
  } while (digitalRead(BUTTON_PIN) || lastbutton);
  beep();
  return selected;
}
//显示APP图标
void DrawApp(int x, byte appID) {
  DrawUIFrame(x, 0, 1);
  drawSlowXYBitmapResize(x + 3, 3, Ico_table[appID], 14, 14, 3, 1);
}
//显示APP对应的文本
void DrawAppText(byte appID) {
  //  arduboy.setCursor(0, 55); arduboy.print(appID);
  if (LANG == 0) arduboy.drawSlowXYBitmap(48, 48, CN_table[appID], 36, 16, 1); else if (LANG == 2 && LANG_JP_State) {
#if LANG_JP_State
    drawText(48, 52, JP_table[appID], pgm_read_byte(&(JP_Length_table[appID])));
#endif
  } else {
    arduboy.setCursor(48, 52);
    arduboy.setTextSize(1);
    Print_EN(appID);
  }
}
void DrawUIFrame(int x, int y, bool color) {
  arduboy.fillRect(x, y, 48, 48, color);
  arduboy.fillRect(x + 3, y + 3, 42, 42, !color); //雕空
  DrawPoint(x, y, 0);
  DrawPoint(x + 47, y, 0);
  DrawPoint(x, y + 47, 0);
  DrawPoint(x + 47, y + 47, 0);
}
void DrawPoint(int x, int y, bool color) {
  arduboy.drawPixel(x + 1, y, color);
  arduboy.drawPixel(x - 1, y, color);
  arduboy.drawPixel(x, y + 1, color);
  arduboy.drawPixel(x, y - 1, color);
  arduboy.drawPixel(x, y, color);
}
//检查按键
void CheckLastButton() {
  if (lastbutton && digitalRead(BUTTON_PIN)) {
    delay(10);
    lastbutton = false;
  }
}
//返回对应层数的对象数
byte QueryMenuObject() {
  int SUM = 0;
  for (int i = 0; i < (MenuLevel); i++) SUM += Menu_table[i];
  return SUM;
}
//信息窗
/*
  void MessageScreen(const char *Items[], uint8_t numberOfItems) {
  lastbutton = (!digitalRead(BUTTON_PIN));

  //u8g.setFont(//u8g_font_9x15);
  //u8g.setFontPosTop();
  for (uint8_t i = 0; i < numberOfItems; i++) //u8g.drawStr( 0, i * 16,  Items[i]);

    do {
      CheckLastButton();
    } while (digitalRead(BUTTON_PIN) || lastbutton);
  beep();
  }
*/
/*
   好看是好看，但是浪费内存
  int wav(byte wavi, int num) {
  return (wavi + byte(millis() / 100)) * (float(float(num - countMin) / float(countMax - countMin)) - 0.5) * 5;
  }
*/
//FP 密集运算屏保
void DrawIntensiveComputing() {
  //关闭加热
#if UsePMOS
  analogWrite(CONTROL_PIN, 0);
#else
  analogWrite(CONTROL_PIN, 255);
#endif
  float calculate;
  // while (1) {
  arduboy.clear();

  //随机线条
  DrawIntensiveComputingLine();

  calculate = sin(millis() / 4000.0);
  //模拟噪点
  for (int i = 0; i < calculate * 256 + 256; i++)  arduboy.drawPixel(random(0, 128), random(0, 64), 1);
  //声效
  if ((beepEnable)) analogWrite(BUZZER_PIN, 64 + calculate * 64 + random(-8, 8));
  //if ((beepEnable)) tone(BUZZER_PIN, int(calculate * 300) + 500 + random(-50, 50));  //没必要浪费内存

  arduboy.display();
  //delay(60-calculate*30);
  //}
}
//绘制屏保-密集运算线条
void DrawIntensiveComputingLine() {
  for (byte a = 0; a < 4; a++) {
    Line[a] += random(-1, 1);
    if (Line[a] > 128) Line[a] -= 128;
    for (byte b = 0; b < random(3, 6); b++) {
      arduboy.drawFastHLine(0, Line[a] + random(-10, 10), 128, 1); //水平线
      arduboy.drawFastVLine(Line[a] + random(-10, 10), 0, 64, 1); //垂直线
    }
  }
}
//模拟数字滚轮 Numerical scrolling effect
void DisplayNum(int Num) {
  arduboy.setTextSize(6);
  SetTextColor(0);
  //数字滚轮
  for (byte i = 0; i < 3; i++) LastValue[i] = int(Value / pow(10, 2 - i)) % 10;
  Value = Num;
  for (byte i = 0; i < 3; i++) {
    SlidingAnimationY[i] += ((int(Value / pow(10, 2 - i)) % 10) - LastValue[i]) * 50;
    if (SlidingAnimationY[i] != 0) SlidingAnimationY[i] += 0.8 * (-SlidingAnimationY[i]);
    arduboy.fillRect(0 + i * 44, 0, 38, 50, 1); //白底
    for (int ii = -1; ii < 2; ii++) {
      arduboy.setCursor(4 + i * 44, 4 - SlidingAnimationY[i] + ii * 50);
      arduboy.print(LastValue[i] + ii);
    }
  }
  //刻度标
  arduboy.fillRect(0, 0, 128, 2, 0); //上遮罩层
  arduboy.fillRect(0, 48, 128, 16, 0); //下遮罩层
}

//数值输入界面
// input value screen
uint16_t InputScreen(byte appID) {
  lastbutton = (!digitalRead(BUTTON_PIN));
  do {
    arduboy.clear();
    DisplayNum(getRotary());
    DrawAppText(appID);
    arduboy.display();
    CheckLastButton();
  } while (digitalRead(BUTTON_PIN) || lastbutton);
  beep();
  return Value;
}
int InputBigNum(int InputPW, byte appID) {
  setRotary(0, 900, 100, InputPW);
  InputPW = InputScreen(appID);
  setRotary(InputPW, InputPW + 90, 10, InputPW);
  InputPW = InputScreen(appID);
  setRotary(InputPW, InputPW + 9, 1, InputPW);
  InputPW = InputScreen(appID);
  return InputPW;
}
void QRcodeScreen() {
  arduboy.clear();
  arduboy.drawSlowXYBitmap(40, 0, QRCode, 48, 48, 1);
  arduboy.display();
  delay(100);
  do {
  } while (digitalRead(BUTTON_PIN) || lastbutton);
  beep();
}
//欠压报警设置
// information display screen
void UnderVoltageSet() {
  setRotary(0, 250, 1, UnderVoltage);
  UnderVoltage = InputScreen(7);
  beep();
}
//设置开机密码
void PasswordSet() {
  Password = InputBigNum(Password, 8);
  beep();
}

void BootPassword() {
  if (Password != 0) {
    do {
      arduboy.clear();
      DrawApp(40, 8);
      DrawAppText(8);
      arduboy.display();
      delay(1000);
      beep(); beep(); beep();
    } while (InputBigNum(0, 8) != Password);
  }
}
//更换预设界面
// change tip screen
void ChangeTipScreen() {
  uint8_t selected = CurrentTip;
  uint8_t lastselected = selected;
  int8_t  arrow = 0;
  if (selected) arrow = 1;
  setRotary(0, NumberOfTips - 1, 1, selected);
  lastbutton = (!digitalRead(BUTTON_PIN));
  do {
    //beep(0);
    arduboy.clear();
    selected = getRotary();
    arrow = constrain(arrow + selected - lastselected, 0, 2);
    lastselected = selected;
    SetTextColor(0);
    arduboy.setTextSize(2);
    arduboy.setCursor(0, 0); arduboy.print(F("Select Tip"));
    SetTextColor(1);
    arduboy.setCursor(0, 16 * (arrow + 1)); arduboy.print(F(">"));
    for (uint8_t i = 0; i < 3; i++) {
      uint8_t drawnumber = selected + i - arrow;
      if (drawnumber < NumberOfTips) {
        arduboy.setCursor(12, 16 * (i + 1)); arduboy.print(TipName[selected + i - arrow]);
      }
    }
    CheckLastButton();
    arduboy.display();
  } while (digitalRead(BUTTON_PIN) || lastbutton);

  beep();
  CurrentTip = selected;
}

//温度校准界面
// temperature calibration screen
void CalibrationScreen() {
  uint16_t CalTempNew[4];
  for (uint8_t CalStep = 0; CalStep < 3; CalStep++) {
    SetTemp = CalTemp[CurrentTip][CalStep];
    setRotary(100, 500, 1, SetTemp);
    beepIfWorky = true;
    lastbutton = (!digitalRead(BUTTON_PIN));
    do {
      arduboy.clear();
      arduboy.setTextSize(2);
      SENSORCheck();      // reads temperature and vibration switch of the iron
      Thermostat();       // heater control
      arduboy.setCursor(0, 0); arduboy.print(F("Step: ")); arduboy.print(CalStep + 1); arduboy.print("/3");
      if (isWorky) {
        arduboy.setCursor(0, 16); arduboy.print(F("Set measured"));
        arduboy.setCursor(0, 32); arduboy.print(F("temp: ")); arduboy.print(getRotary());
      } else {
        arduboy.setCursor(0, 16); arduboy.print(F("ADC: ")); arduboy.print(uint16_t(RawTemp));
        arduboy.setCursor(0, 32); arduboy.print(F("Please wait"));
      }
      CheckLastButton();
      arduboy.display();
    } while (digitalRead(BUTTON_PIN) || lastbutton);

    CalTempNew[CalStep] = getRotary();
    beep(); delay (10);
  }

  //关闭加热
#if UsePMOS
  analogWrite(CONTROL_PIN, 0);
#else
  analogWrite(CONTROL_PIN, 255);
#endif
  delayMicroseconds(time2settle);             // wait for voltage to settle
  CalTempNew[3] = getChipTemp();              // read chip temperature
  if ((CalTempNew[0] + 30 < CalTempNew[1]) && (CalTempNew[1] + 30 < CalTempNew[2])) {
    MenuLevel = 7;
    if (MenuScreen(0)) {
      for (uint8_t i = 0; i < 4; i++) CalTemp[CurrentTip][i] = CalTempNew[i];
    }
  }
}

//命名界面 文本输入界面
// input tip name screen
void InputNameScreen() {
  uint8_t  value;
  for (uint8_t digit = 0; digit < (TIPNAMELENGTH - 1); digit++) {
    lastbutton = (!digitalRead(BUTTON_PIN));
    setRotary(31, 96, 1, 65);
    do {
      value = getRotary();
      if (value == 31) {
        value = 95;
        setRotary(31, 96, 1, 95);
      }
      if (value == 96) {
        value = 32;
        setRotary(31, 96, 1, 32);
      }
      //arduboy.setCursor(0, 0);arduboy.print();
      arduboy.clear();
      arduboy.setTextSize(2);
      arduboy.setCursor(16 * digit, 48); arduboy.print(char(94));
      arduboy.setCursor(0, 32);
      for (uint8_t i = 0; i < digit; i++) arduboy.print(TipName[CurrentTip][i]);
      arduboy.setCursor(16 * digit, 32); arduboy.print(char(value));
      CheckLastButton();
      arduboy.display();
    } while (digitalRead(BUTTON_PIN) || lastbutton);
    TipName[CurrentTip][digit] = value;
    beep(); delay (10);
  }
  TipName[CurrentTip][TIPNAMELENGTH - 1] = 0;
  return value;
}


// delete tip screen
void DeleteTipScreen() {
  MenuLevel = 7;
  if (NumberOfTips == 1) {
    //MessageScreen(DeleteMessage, sizeof(DeleteMessage));
  }
  else if (MenuScreen(0)) {
    if (CurrentTip == (NumberOfTips - 1)) {
      CurrentTip--;
    }
    else {
      for (uint8_t i = CurrentTip; i < (NumberOfTips - 1); i++) {
        for (uint8_t j = 0; j < TIPNAMELENGTH; j++) TipName[i][j] = TipName[i + 1][j];
        for (uint8_t j = 0; j < 4; j++)             CalTemp[i][j] = CalTemp[i + 1][j];
      }
    }
    NumberOfTips--;
  }
}


// add new tip screen
void AddTipScreen() {
  if (NumberOfTips < TIPMAX) {
    CurrentTip = NumberOfTips++; InputNameScreen();
    CalTemp[CurrentTip][0] = TEMP200; CalTemp[CurrentTip][1] = TEMP280;
    CalTemp[CurrentTip][2] = TEMP360; CalTemp[CurrentTip][3] = TEMPCHP;
  } //MessageScreen(MaxTipMessage, sizeof(MaxTipMessage)); 信息窗
}


// average several ADC readings in sleep mode to denoise
uint16_t denoiseAnalog (byte port) {
  uint16_t result = 0;
  ADCSRA |= bit (ADEN) | bit (ADIF);    // enable ADC, turn off any pending interrupt
  if (port >= A0) port -= A0;           // set port and
  ADMUX = (0x0F & port) | bit(REFS0);   // reference to AVcc
  set_sleep_mode (SLEEP_MODE_ADC);      // sleep during sample for noise reduction
  for (uint8_t i = 0; i < 32; i++) {    // get 32 readings
    sleep_mode();                       // go to sleep while taking ADC sample
    while (bitRead(ADCSRA, ADSC));      // make sure sampling is completed
    result += ADC;                      // add them up
  }
  bitClear (ADCSRA, ADEN);              // disable ADC
  return (result >> 5);                 // devide by 32 and return value
}

/*
  //读取芯片温度
  // get internal temperature by reading ADC channel 8 against 1.1V reference
  double getChipTemp() {
  unsigned int wADC;
  double t;
  ADMUX = (_BV(REFS1) | _BV(REFS0) | _BV(MUX3));
  ADCSRA |= _BV(ADEN);
  delay(5);
  ADCSRA |= _BV(ADSC);
  while (bit_is_set(ADCSRA, ADSC));
  wADC = ADCW;
  t = (wADC - ChipTempCalVal ) / 1.22;
  return (t);
  }
*/
// get internal temperature by reading ADC channel 8 against 1.1V reference
double getChipTemp() {
  uint16_t result = 0;
  ADCSRA |= bit (ADEN) | bit (ADIF);    // enable ADC, turn off any pending interrupt
  ADMUX = bit (REFS1) | bit (REFS0) | bit (MUX3); // set reference and mux
  delay(10);                            // wait for voltages to settle
  set_sleep_mode (SLEEP_MODE_ADC);      // sleep during sample for noise reduction
  for (uint8_t i = 0; i < 32; i++) {    // get 32 readings
    sleep_mode();                       // go to sleep while taking ADC sample
    while (bitRead(ADCSRA, ADSC));      // make sure sampling is completed
    result += ADC;                      // add them up
  }
  bitClear (ADCSRA, ADEN);              // disable ADC
  result >>= 2;                         // devide by 4
  return ((result - 2594) / 9.76);      // calculate internal temperature in degrees C
}

// get input voltage in mV by reading 1.1V reference against AVcc
uint16_t getVCC() {
  uint16_t result = 0;
  ADCSRA |= bit (ADEN) | bit (ADIF);    // enable ADC, turn off any pending interrupt
  // set Vcc measurement against 1.1V reference
  ADMUX = bit (REFS0) | bit (MUX3) | bit (MUX2) | bit (MUX1);
  delay(1);                             // wait for voltages to settle
  set_sleep_mode (SLEEP_MODE_ADC);      // sleep during sample for noise reduction
  for (uint8_t i = 0; i < 16; i++) {    // get 16 readings
    sleep_mode();                       // go to sleep while taking ADC sample
    while (bitRead(ADCSRA, ADSC));      // make sure sampling is completed
    result += ADC;                      // add them up
  }
  bitClear (ADCSRA, ADEN);              // disable ADC
  result >>= 4;                         // devide by 16
  return (1125300L / result);           // 1125300 = 1.1 * 1023 * 1000
}


// get supply voltage in mV
uint16_t getVIN() {
  long result;
  result = denoiseAnalog (VIN_PIN);     // read supply voltage via voltage divider
  return (result * Vcc / 179.474);      // 179.474 = 1023 * R13 / (R12 + R13)
}

//ADC中断服务
// ADC interrupt service routine
EMPTY_INTERRUPT (ADC_vect);             // nothing to be done here

//旋转编码器触发中断
// Pin change interrupt service routine for rotary encoder
ISR (PCINT0_vect) {
  uint8_t a = PINB & 1;
  uint8_t b = PIND >> 7 & 1;
  if (a != a0) {              // A changed
    a0 = a;
    if (b != b0) {            // B changed
      b0 = b;
      count = constrain(count + ((a == b) ? countStep : -countStep), countMin, countMax);
      if (ROTARY_TYPE && ((a == b) != ab0)) {
        count = constrain(count + ((a == b) ? countStep : -countStep), countMin, countMax);;
      }
      ab0 = (a == b);
      handleMoved = true;
    }
  }
}

//显示位图，并允许放大 代码片段改自arduboy2
void drawSlowXYBitmapResize(int x, int y, const uint8_t *bitmap, uint8_t w, uint8_t h, uint8_t size, uint8_t color) {
  // no need to draw at all of we're offscreen
  /*
    if (x + w < 0 || x > WIDTH - 1 || y + h < 0 || y > HEIGHT - 1)
    return;
  */
  int16_t xi, yi, byteWidth = (w + 7) / 8;
  for (yi = 0; yi < h; yi ++) {
    for (xi = 0; xi < w; xi ++) {
      if (pgm_read_byte(bitmap + yi * byteWidth + xi / 8) & (128 >> (xi & 7))) {
        //arduboy.drawPixel(x + xi, y + yi, color);
        arduboy.fillRect(x + xi * size, y + yi * size, size, size, color);
      }
    }
  }
}

//设置看门狗模式-中断+复位
void SetWDT() {
  byte bb;
  bb = 7 & 7;
  bb |= (1 << WDCE);

  __asm__ __volatile__ ("wdr");       //看门狗复位
  MCUSR &= ~(1 << WDRF);              //MUUSR中的WDRF清零，清除复位标志
  WDTCSR |= (1 << WDCE) | (1 << WDE); //打开允许修改使能，并WDE置1
  //设置新的看门狗超时值bb
  WDTCSR = bb;
  WDTCSR |= _BV(WDIE);                //设置中断模式
  WDTCSR |= _BV(WDE);                 //设置复位模式
}

/*
  8x8 dot Japanese font for Arduboy

  Copyright (c) 2016 emutyworks

  Released under the MIT license
  https://github.com/emutyworks/8x8DotJPFont/blob/master/LICENSE.txt
*/
#if LANG_JP_State
void drawText(uint8_t x, uint8_t y, const uint8_t *mes, uint8_t cnt)
{
  uint8_t pb;
  uint8_t page;
  uint8_t screen_start = 0;
  uint8_t screen_end = 128;

  if (x < screen_start) {
    x = screen_start;
  }

  for (uint8_t i = 0; i < cnt; i++) {
    pb = pgm_read_byte_near(mes + i);

    switch (pb) {
      case MISAKI_FONT_F0_PAGE:
        page = MISAKI_FONT_F0_PAGE;
        continue;
      case MISAKI_FONT_F1_PAGE:
        page = MISAKI_FONT_F1_PAGE;
        continue;
      case MISAKI_FONT_F2_PAGE:
        page = MISAKI_FONT_F2_PAGE;
        continue;
    }

    if (!page) {
      continue;
    }

    switch (page) {
#ifdef MISAKI_FONT_F0_H
      case MISAKI_FONT_F0_PAGE:
        if (pb > MISAKI_FONT_F0_SIZE) {
          continue;
        }
        if ((x + 8) > screen_end) {
          x = screen_start;
          y = y + 8;
        }
        arduboy.drawBitmap(x, y,  misaki_font_f0[ pb ], MISAKI_FONT_F0_W, 8, WHITE);
        x = x + 8;
        break;
#endif
#ifdef MISAKI_FONT_F1_H
      case MISAKI_FONT_F1_PAGE:
        if (pb > MISAKI_FONT_F1_SIZE) {
          continue;
        }
        if ((x + 4) > screen_end) {
          x = screen_start;
          y = y + 8;
        }
        arduboy.drawBitmap(x, y,  misaki_font_f1[ pb ], MISAKI_FONT_F1_W, 8, WHITE);
        arduboy.drawBitmap(x + 3, y, misaki_font_0x00, 1, 8, WHITE);
        x = x + 4;
        break;
#endif
#ifdef MISAKI_FONT_F2_H
      case MISAKI_FONT_F2_PAGE:
        if (pb > MISAKI_FONT_F2_SIZE) {
          continue;
        }
        if ((x + 8) > screen_end) {
          x = screen_start;
          y = y + 8;
        }
        arduboy.drawBitmap(x, y,  misaki_font_f2[ pb ], MISAKI_FONT_F2_W, 8, WHITE);
        arduboy.drawBitmap(x + 7, y, misaki_font_0x00, 1, 8, WHITE);
        x = x + 8;
        break;
#endif
    }
  }
}
#endif
